ANTMAN2021/MICROMOUSE/Images/IMG-20240708-WA0026.jpg

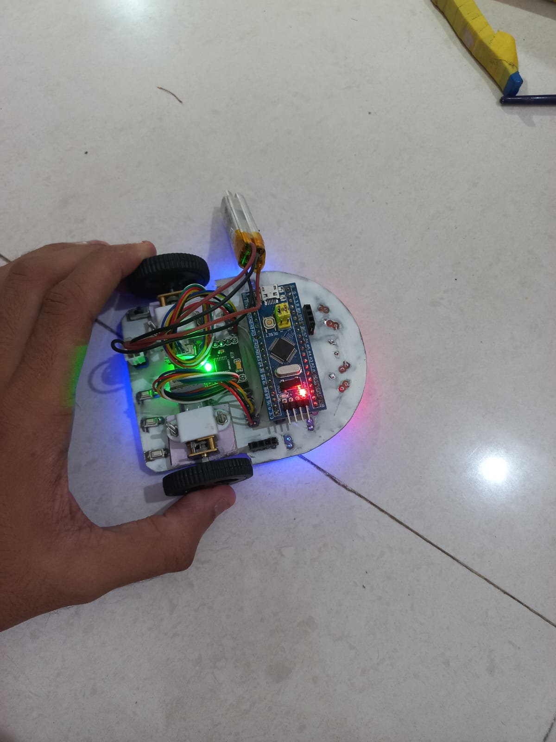
Images/IMG-20240708-WA0026.jpg
